itsadisood/SWIPE-STACK/STM32 Code/HUB75/inc/game_driver.h

#ifndef __GAME_DRIVER__
#define __GAME_DRIVER__

#include "hub75_driver.h"

// M
#define STEP 2

// Game board dimensions
#define BOARD_TOP 41
#define BOARD_R 20
#define BOARD_C 40

// Bit mask to define HUB75_R with col pixels of Game board
#define ROW_MASK 0x3fffffffffc


volatile bool KEY_LEFT;
volatile bool KEY_ROT;
volatile bool KEY_RIGHT;
volatile bool ROTATE;

// fall time for blocks
volatile uint32_t fall_time;


void game_init (pixel_t * screen);

void init_hub(pixel_t * screen);

void clear_row (pixel_t * screen, int y);

void drop_rows (pixel_t * screen, int row);

void setup_adc (void);

void set_random_seed ();

void setup_tim3(uint32_t psc, uint32_t arr); // setup game timer

void init_exti();

void sr_coord_board (pixel_t * screen, coord_t * positions, hub75_color_t color, bool set);


// IRQ Handlers
extern void EXTI0_1_IRQHandler();
extern void EXTI2_3_IRQHandler();
extern void EXTI4_15_IRQHandler();
extern void TIM3_IRQHandler();

#endif
