itsadisood/SWIPE-STACK/STM32 Code/HUB75/inc/oled_driver.h

#include "typeface.h"

void setup_oled();

void setupGPIO_spi();

void init_spi1();

void spi1_init_display();

void spi1_setup_dma();

void updt_score(char * scoreBuff, char * levelBuff);

void init_score();
